tamago324/EvoRoll/v3/stl/evoroll_v3_bottom.stl

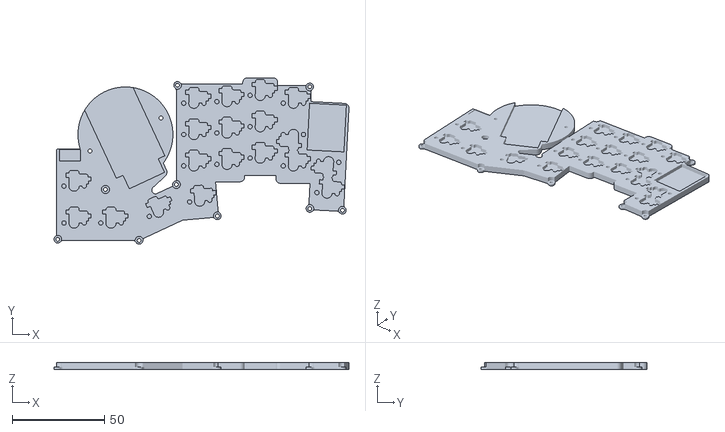
[picture p21: CAD file, 2024-10-31, an earlier design]
v3/stl/evoroll_v3_bottom.stl
160.0 x 90.2 x 3.80
