tamago324/EvoRoll/v1/dxf/pcb_edge.dxf

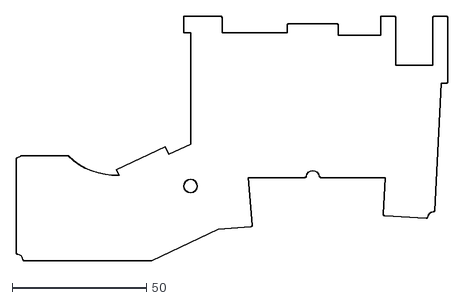
[picture p22: CAD file, 2024-09-05, an earlier design]
v1/dxf/pcb_edge.dxf
160.7 x 91.0
