tamago324/EvoRoll/v1/stl/evoroll_v1_bottom_case.stl

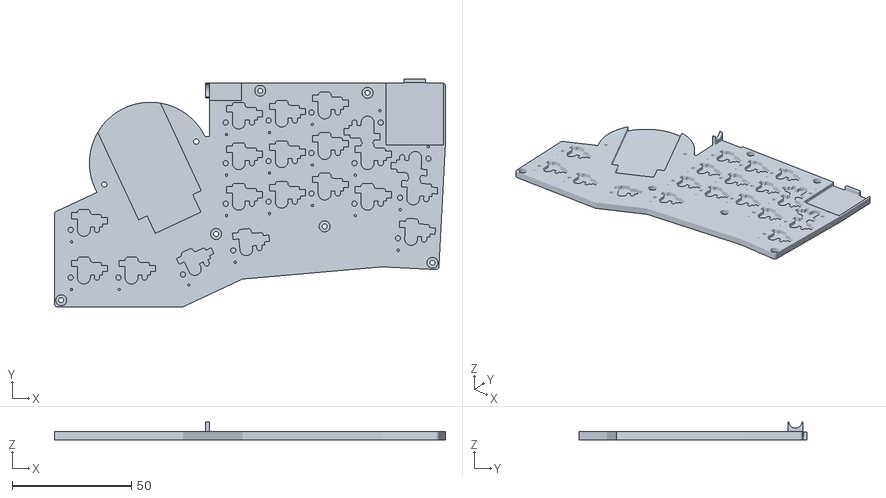
[picture p23: CAD file, 2024-09-05, an earlier design]
v1/stl/evoroll_v1_bottom_case.stl
163.9 x 95.5 x 7.40
