tamago324/EvoRoll/v2/dxf/evoroll_v2_support.dxf

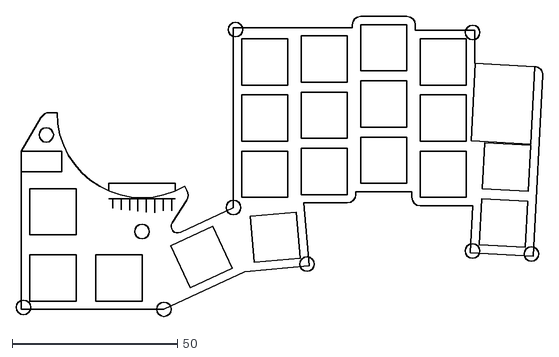
[picture p24: CAD file, 2024-10-14, an earlier design]
v2/dxf/evoroll_v2_support.dxf
159.3 x 90.8
